KarolPtak/HelixMidi/midi-controller/Looper2Page.cpp

#include "BasePage.h"
#include "globals.h"
#include <MIDI.h>

    Looper2Page::Looper2Page() {
      active = false;
      recording = false;
    }

    int Looper2Page::id() {
      return LOOPER2PAGE;
    }
    void Looper2Page::button1Action() {
        digitalWrite(LED_PIN, active); //that's only for debugging

        active = false;
        recording = false;
        MIDI.sendControlChange(midiCcLooperPlayStop, midiLowValue, midiChannel); //Send stop signal, stop recording
        
        updateLedStrip(); 
    }
    void Looper2Page::button2Action(boolean longPress) {
      if(longPress) {
        tunerAction();
        return;
      }
      
      //undo/redo has a bit more complex behaviour, so it may cause the state of active/recording, and the state of looper in the stomp to be not in sync
      MIDI.sendControlChange(midiCcLooperUndo, midiHighValue, midiChannel); 
    }
    void Looper2Page::button3Action() {
        active = true;
        recording = false;
        MIDI.sendControlChange(midiCcLooperPlayStop, midiHighValue, midiChannel); //Send play signal, turn on looper or stop recording

        updateLedStrip();
    }
    void Looper2Page::button4Action() {
        if (!active){
            active = true;
            recording = true;
            MIDI.sendControlChange(midiCcLooperRecordOverdub, midiHighValue, midiChannel); //Send record signal, turn on looper and start recording
        }
        else{
            recording = true;
            MIDI.sendControlChange(midiCcLooperRecordOverdub, midiLowValue, midiChannel); //Send overdub signal, start overdubbing
        }
        updateLedStrip();
    }
    void Looper2Page::setup() { //setup when page is changed to this
      updateLedStrip();
    }
        
    void Looper2Page::updateLedStrip() {
        colors[0] = hsvToRgb(looperPageHue,   looperPageSat, active == false ? ledDim : ledBright);
        colors[1] = hsvToRgb(looperPageHue,   looperPageSat, active == false ? ledDim : ledBright);
        colors[2] = hsvToRgb(looperPageHue,   looperPageSat, ledDim);
        colors[3] = hsvToRgb(tunerHue,        tunerSat, ledDim);
        colors[4] = hsvToRgb(looperPageHue,   looperPageSat, active == false ? ledDim : ledBright);
        colors[5] = hsvToRgb(looperPageHue,   looperPageSat, active == false ? ledDim : ledBright);
        colors[6] = hsvToRgb(looperRecordHue, looperRecordSat, recording == false ? ledDim : ledBright);
        colors[7] = hsvToRgb(looperRecordHue, looperRecordSat, recording == false ? ledDim : ledBright);

        ledStrip.write(colors, LED_COUNT);  
    }   
